theorlangur/nrf_presence/src/ld2412_task.hpp

#ifndef LD2412_TASK_HPP_
#define LD2412_TASK_HPP_

#include <optional>
#include <variant>
#include <nrf_general/lib_msgq_typed.hpp>
#include <nrf_uart/periphery/lib_ld2412.hpp>

namespace ld2412
{
    enum class err_t
    {
        Ok,
        Restart,
        ReloadConfig,
        FactoryReset,
        Bluetooth,
        SetBasicCfg,
        SetLightSenseCfg,
        SetEnergyThresholds,
        RunBackAnalysis,
        ConfigureCollectStatistics,
        SnapshotStatistics,
        EnergyModeAfterBackAnalysis
    };

    enum class notification_id_t: uint8_t
    {
        BackgroundAnalysisDone
        , BackgroundAnalysisError
        , SetBasicCfgDone
        , SetLightSenseDone
        , SetEnergyThresholdsDone
    };

    struct basic_cfg_t{
        hlk::LD2412::DistanceRes resolution = hlk::LD2412::DistanceRes::_0_50;
        uint8_t gate_from = 0;
        uint8_t gate_to = 13;
        uint16_t clear_delay = 0;
    };
    struct light_sense_cfg_t{
        hlk::LD2412::LightSensitivity mode = hlk::LD2412::LightSensitivity::Off;;
        uint8_t threshold = 0;
    };
    struct still_thresholds_cfg_t{
        hlk::LD2412::gate_array_t const& still_thresholds;
    };
    struct move_thresholds_cfg_t{
        hlk::LD2412::gate_array_t const& move_thresholds;
    };
    struct run_background_analysis_t{
        enum class Result
        {
            Ok,
            Failed
        };
        using callback_t = void(*)(Result result);
        callback_t cb;
    };
    struct collect_statistics_cfg_t{
        uint8_t window_size = 0;//samples 0 -> off
    };
    struct snapshot_statistics_cfg_t{
        using callback_t = void(*)(hlk::LD2412::energy_stat_array_t const& still, hlk::LD2412::energy_stat_array_t const& move);
        callback_t cb;
    };
    struct restart_cfg_t{};
    struct reload_cfg_t{};
    struct factory_reset_cfg_t{};
    struct bt_cfg_t{bool on;};
    struct start_analysis_for_presence_t{};
    struct start_analysis_for_absence_t{};
    struct stop_analysis_t{};

    using QueueItem = std::variant<
        restart_cfg_t
        , reload_cfg_t
        , factory_reset_cfg_t
        , bt_cfg_t
        , basic_cfg_t
        , light_sense_cfg_t
        , still_thresholds_cfg_t
        , move_thresholds_cfg_t
        , run_background_analysis_t
        , collect_statistics_cfg_t
        , snapshot_statistics_cfg_t
        , start_analysis_for_presence_t
        , start_analysis_for_absence_t
        , stop_analysis_t
    >;
    using Queue = msgq::Queue<QueueItem,4>;

    class Instance
    {
    public:
        using err_callback_t = void(*)(err_t);
        using notify_callback_t = void(*)(notification_id_t);

        Instance(Queue &q, const struct device *uart, const char* thread_name);

        hlk::LD2412* setup(err_callback_t err, notify_callback_t notification, uint8_t idx, volatile uint8_t &flags);
        hlk::LD2412* sensor();

        void restart();
        void reload_config();
        void factory_reset();
        void switch_bluetooth(bool on);
        void set_basic_config(basic_cfg_t const& cfg);
        void set_light_sense(light_sense_cfg_t const& cfg);
        void set_still_thresholds(still_thresholds_cfg_t const& cfg);
        void set_move_thresholds(move_thresholds_cfg_t const& cfg);
        void set_still_thresholds_raw(hlk::LD2412::gate_array_t const& thr) { set_still_thresholds(still_thresholds_cfg_t{.still_thresholds = thr}); }
        void set_move_thresholds_raw(hlk::LD2412::gate_array_t const& thr) { set_move_thresholds(move_thresholds_cfg_t{.move_thresholds = thr}); }
        void run_back_analysis(run_background_analysis_t const& cfg);
        void collect_statistics(uint8_t win_size);
        void take_statistic_snapshot(snapshot_statistics_cfg_t const& cfg);

        void start_analysis_for_presence(start_analysis_for_presence_t const& cfg);
        void start_analysis_for_absence(start_analysis_for_absence_t const& cfg);
        void stop_analysis(stop_analysis_t const& cfg);
        void get_analysis_results(hlk::LD2412::gate_array_t &results);

        auto get_stat_collect_window_size() const { return m_StatSampleCount; }
        bool is_running_back_analysis() const { return m_BackgroundAnalysisDoneCB != nullptr; }
    private:
        void mainloop();
        void collect_sample();
        void check_back_analysis();

        enum AnalysisState
        {
            Stopped,
            RunningForPresence,
            RunningForAbsence,
        };

        /**********************************************************************/
        /* Thread-related stuff                                               */
        /**********************************************************************/
        static void thread_func(void *, void *, void *);

        static constexpr uint8_t MAX_STAT_SAMPLE_SIZE = 255;
        static constexpr size_t THREAD_STACK_SIZE = 1024 * 2;
        static constexpr size_t THREAD_PRIORITY=7;

        alignas(16) k_thread_stack_t m_ThreadStack[THREAD_STACK_SIZE];
        k_thread m_Thread;
        const char *m_ThreadName = nullptr;
        k_tid_t m_ThreadID = {};

        /**********************************************************************/
        /* End of thread-related stuff                                        */
        /**********************************************************************/
        Queue &m_Q;
        const struct device *m_pUART;
        hlk::LD2412 m_Sensor;

        err_callback_t m_ErrCB = nullptr;
        notify_callback_t m_NotifyCB = nullptr;

        run_background_analysis_t::callback_t m_BackgroundAnalysisDoneCB = {};

        struct stat_sample_t
        {
            hlk::LD2412::gate_array_t still_energies;
            hlk::LD2412::gate_array_t move_energies;
        };

        stat_sample_t m_StatSampleBuffer[MAX_STAT_SAMPLE_SIZE];
        size_t m_StatSampleIndex = 0;
        size_t m_StatSampleCount = 0;
        size_t m_TotalSamplesWritten = 0;
        size_t m_FrameReadErrorCount = 0;

        size_t m_LightSensorUpdateInterval = 5;//seconds

        AnalysisState m_Analysis = AnalysisState::Stopped;
        hlk::LD2412::gate_array_t m_AnalysisStillEnergies;
        uint8_t m_Idx = 0;
        volatile uint8_t *m_pFlags = nullptr;
    };
}
#endif
